igorwolfs/acoustic-material-characterization/acoustic-carrier-hw/simulations/schematics/cc12_schmitt_trigger.asc

C1: cap; 10pF
C2: cap; 10pF
C3: cap; 10pF
C4: cap; 10nF
C5: cap; 10nF
C6: cap; 10nF
D1: diode
D2: diode
D3: diode
R1: res; 1k
R2: res; 2e6
R3: res; 51k
R4: res; 100k
R5: res; 1k
R6: res; 5.1k
R7: res; 6.2k
R8: res; 1.2k
R9: res; 2e6
R10: res; 100k
R11: res; 1k
R12: res; 1k
R13: res; 21k
R14: res; 5.1k
R15: res; 2e6
R16: res; 100k
R17: res; 1k
R18: res; 1k
R19: res; 4.7k
R20: res; 47
R21: res; 47
R22: res; 47
U1: Comparator_ST
U2: Comparator_ST
U3: Comparator_ST
V1: voltage; SINE(5 1 20)
V2: voltage; 2
V3: voltage; 2
V4: voltage; 5
V5: voltage; SINE(5 1 20)
V6: voltage; 2
V7: voltage; SINE(0.7 0.35 1)
Named nets: 0, VBUS, Vref
.tran 0 3 0 1e-4
SIMPLE COMPARATOR WITH SINUSOIDAL SOURCE
COMPARATOR WITH HIGH VOLTAGE DIVIDER
COMPARATOR WITH LOW VOLTAGE DIVIDER
