igorwolfs/acoustic-material-characterization/acoustic-carrier-hw/simulations/schematics/adc_analog_input.asc

C1: cap; {C_P}
C2: cap; {C_P}
C3: cap; {C_H}
C4: cap; {C_H}
C7: cap; {C_block}
C8: cap; {C_filter}
C9: cap; {C_block}
L1: ind; {{L_filter} + 0.05*{L_filter}}
L2: ind; {{L_filter}-0.05*{L_filter}}
R1: res; {R_tl}
R2: res; {R_tl}
R3: res; {R_diff}
R4: res; {R_diff/2}
R5: res; {R_diff/2}
R6: res; {R_div}
R7: res; {R_div}
R8: res; 100e3
R9: res; 100e3
R10: res; 5
R11: res; 5
S1: sw; SW1
S2: sw; SW1
S3: sw; SW1
S4: sw; SW1
U1: UniversalOpAmp; Avol=1000 GBW=2e20 Vos=0
U2: UniversalOpAmp; Avol=1000 GBW=2e20 Vos=0
V1: voltage; PULSE(0 3.3 0 2.14e-9 2.14e-9 10e-9 28.57e-9 1e6)
V2: voltage; PULSE(3.3 0 0 2.14e-9 2.14e-9 10e-9 28.57e-9 1e6)
V3: voltage; SINE(0 1.5 1e6 0 0 0 1e6); AC 1 0; Rser=0
V4: voltage; 3.3
Named nets: AIN+, AIN-, 0, V_IN_SW, V_SHA_SW, V_bias, VREF
.param C_P=5e-9 C_H=5e-9 t_rf=2.14e-9 tch=10e-9 C_block=100e-9 R_diff=100 R_tl=1 R_div=4.7e3 L_filter=100nH C_filter=100pF
.tran 0 10e-6 0 1e-10
CLK_LOW:
- SW1, SW2: closed, SW3: open
- Ch is charged
CLK LOW->HIGH:
- SW1, SW2: opened, SW3: closed
- SHA in HOLD mode
a few moments later
- SW3 closed
- Amplifier output == CH voltage
.model SW1 SW(Ron=1 Roff=1e9 Vt=1.5 Vh=0)
Ideal buffering OPAMP 
- SHORT between 2 inputs
- infinite input impedance
Note: in order to buffer a differential signals we need 2 buffers
Input impedance for next stage
.ac oct 1e3 1e3 15e6
NOTES ON DIFFERENTIAL VS SINGLE-ENDED FILTERS
Differential filter
- differential impedance Zd(f) (to differential component: Vd = V+ - V-)
- common mode impedance infinity (to common-mode component (V+ + V-) / 2) 
- So the filter acts purely on the differential mode.
- Ground variations only affect common-mode voltage, not the filtered differential voltage
Single-ended filter
- Filters signal w.r.t. ground -> single-ended signals take this path back to source.
- Stray currents can change the filter's behavior and the line voltage
