igorwolfs/acoustic-material-characterization/acoustic-piezodriver-hw/simulations/schematics/sepic_5V_carrier.asc

C1: cap; 1�F
C2: cap; 100pF
C3: cap; 318e-9
C4: cap; 5.4e-9
C5: cap; 100pF
C_in: cap; 100�F
C_out: cap; 100�F
D1: schottky; SS24
L1: ind; 60�H
L2: ind; 60�H
L3: ind; 1nF; Rser=1
M2: nmos; IRLML6344
R1: res; 40k
R2: res; 60k
R3: res; 1.80e3
R4: res; 0.1
R5: res; 0.01
R6: res; 20
R7: res; 8.6k
U2: LM3478_TRANS
V1: voltage; 5
Named nets: 0
.tran 0 100e-3 0 1e-6
DIODE: SS24 -> Should be SS14
FET: Choose between AO3400A or SI7454DP
